howardt12345/keyboard0/PCB/Gerber/Draft 1-1/custom_keyboard (f303, fe2.1) bottom with fill.png

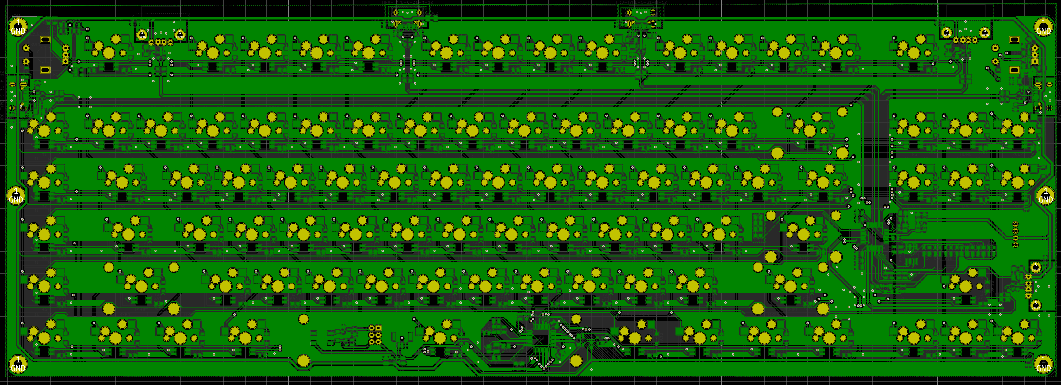
PCB/Gerber/Draft 1-1/custom_keyboard (f303, fe2.1) bottom with fill.png
