howardt12345/keyboard0/PCB/Gerber/Draft 1-2/Images/custom_keyboard (f303, fe2.1) bottom 3d.png

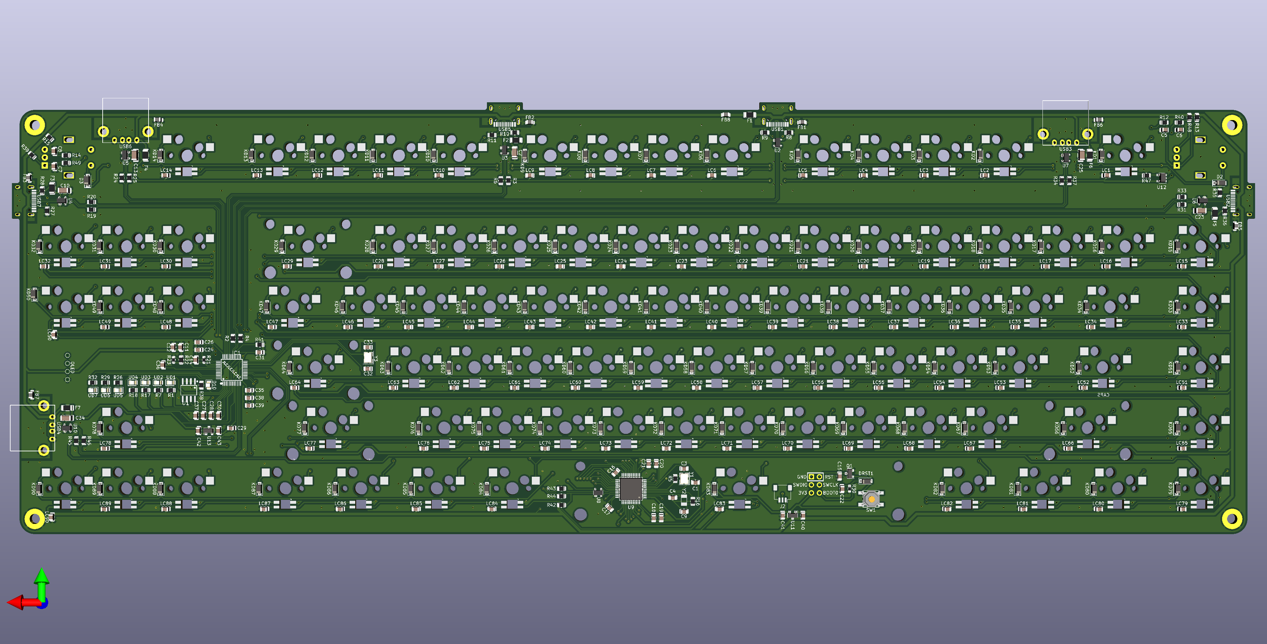
PCB/Gerber/Draft 1-2/Images/custom_keyboard (f303, fe2.1) bottom 3d.png
