howardt12345/keyboard0/PCB/Gerber/Draft 1-2/Images/custom_keyboard (f303, fe2.1) top high contrast.png

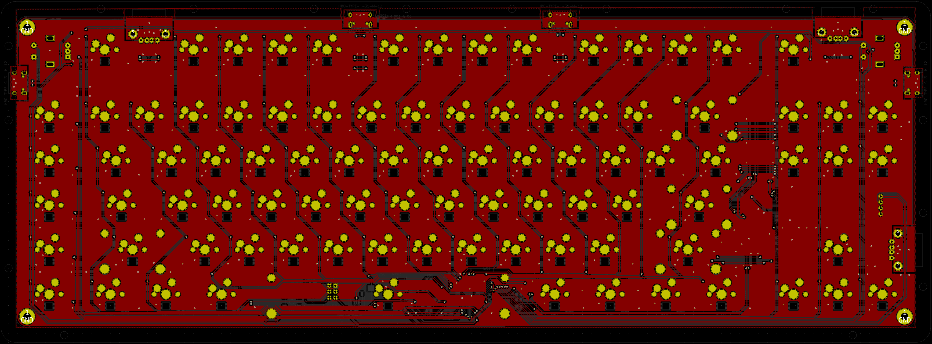
PCB/Gerber/Draft 1-2/Images/custom_keyboard (f303, fe2.1) top high contrast.png
