howardt12345/keyboard0/PCB/Gerber/Draft 1-3/Images/2021-10-26/custom_keyboard (f303, fe2.1) bottom 3d.png

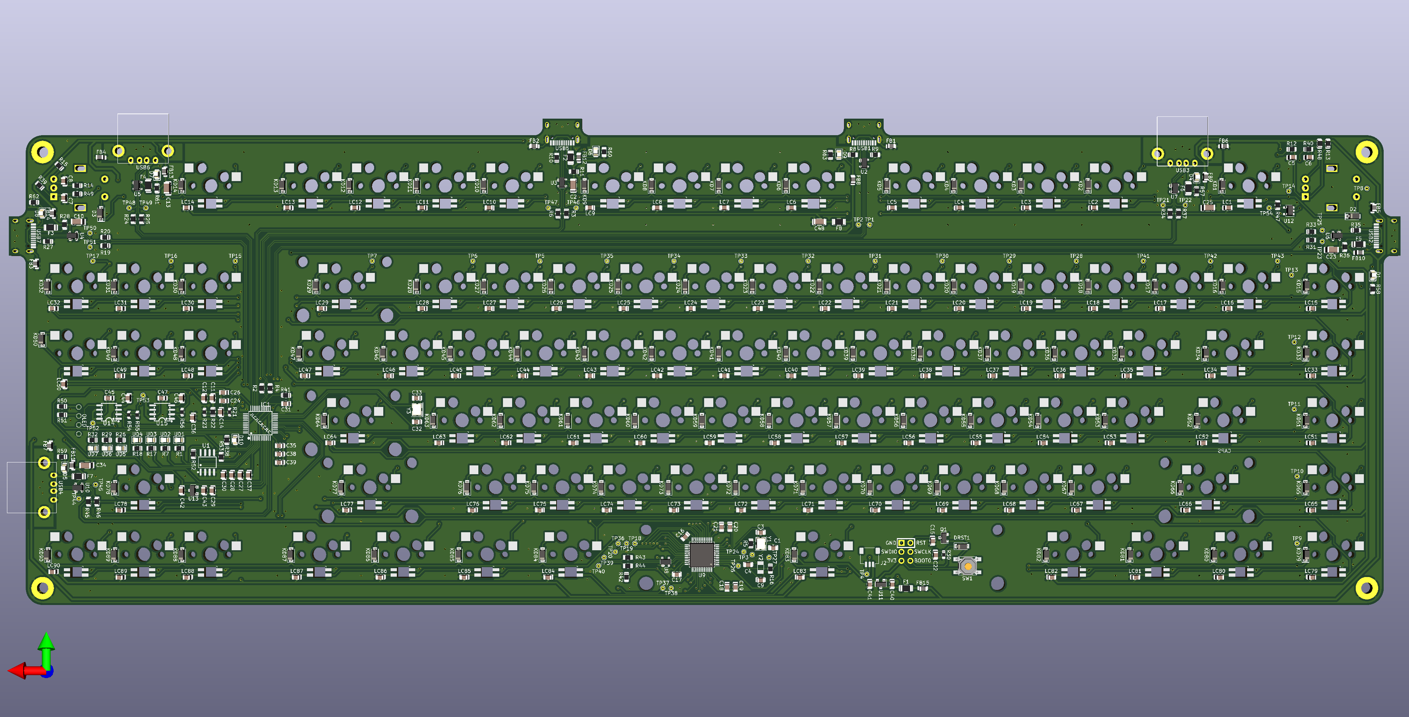
PCB/Gerber/Draft 1-3/Images/2021-10-26/custom_keyboard (f303, fe2.1) bottom 3d.png
