howardt12345/keyboard0/PCB/Gerber/Draft 1-4/Images/2021-10-29/custom_keyboard (f103, fe2.1) bottom fill.png

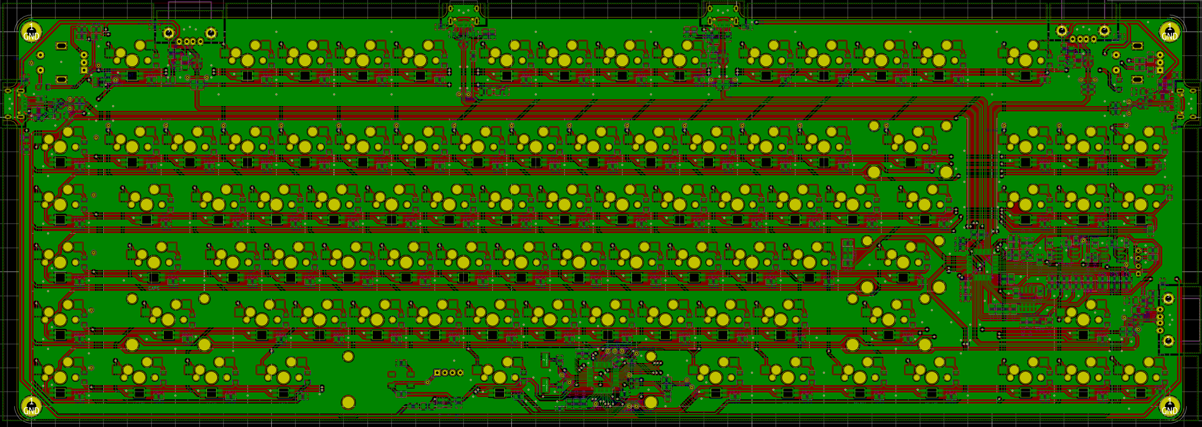
PCB/Gerber/Draft 1-4/Images/2021-10-29/custom_keyboard (f103, fe2.1) bottom fill.png
