howardt12345/keyboard0/PCB/p2/Pics/2.1/keyboard0 bottom.png

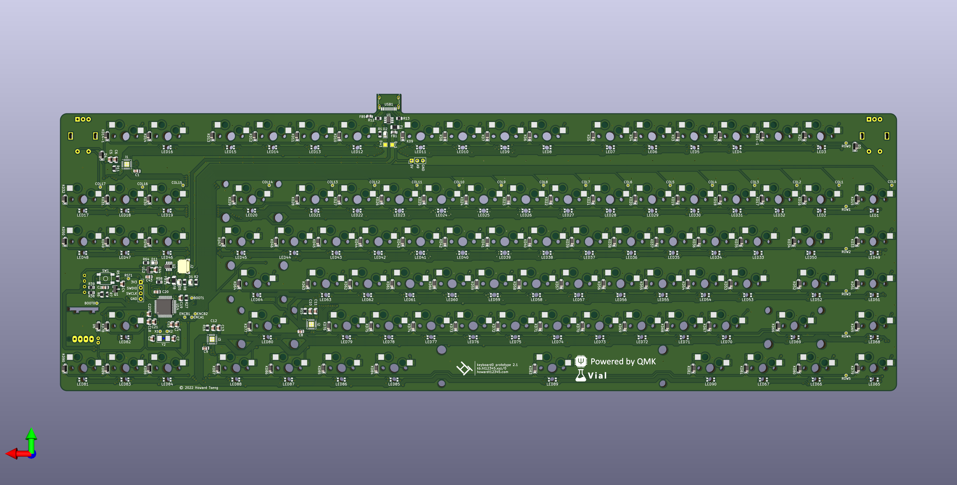
PCB/p2/Pics/2.1/keyboard0 bottom.png
