howardt12345/keyboard0/PCB/p2/Pics/custom_keyboard (f303).png

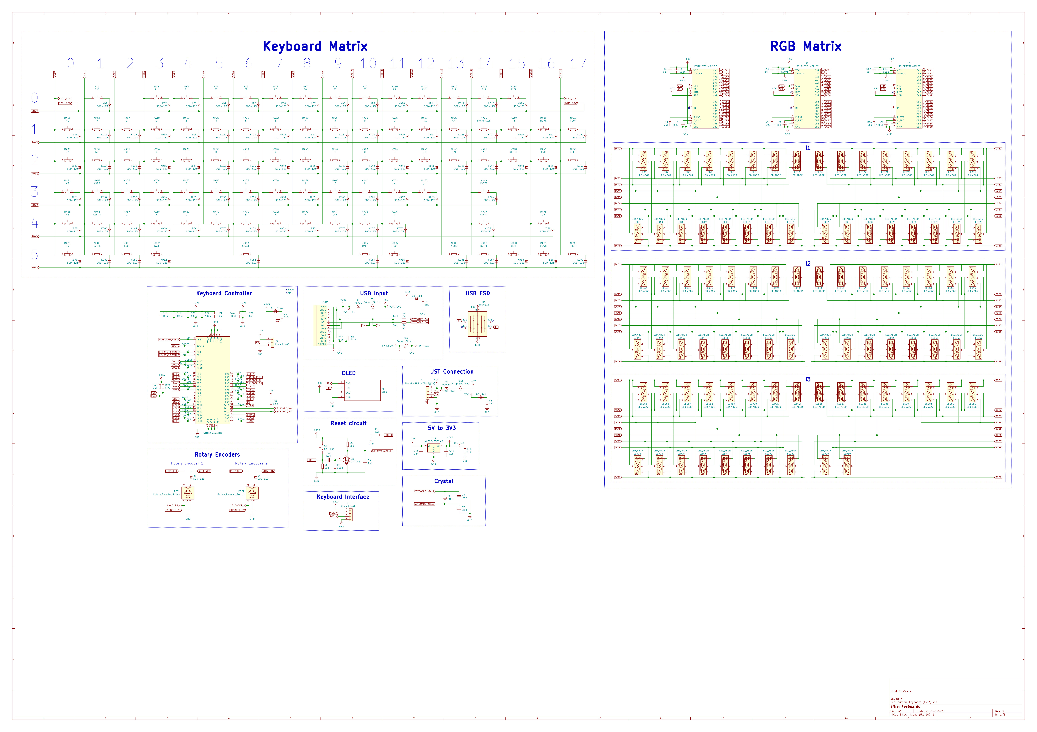
PCB/p2/Pics/custom_keyboard (f303).png
