howardt12345/keyboard0/PCB/p2/Pics/custom_keyboard bottom 3d (1).png

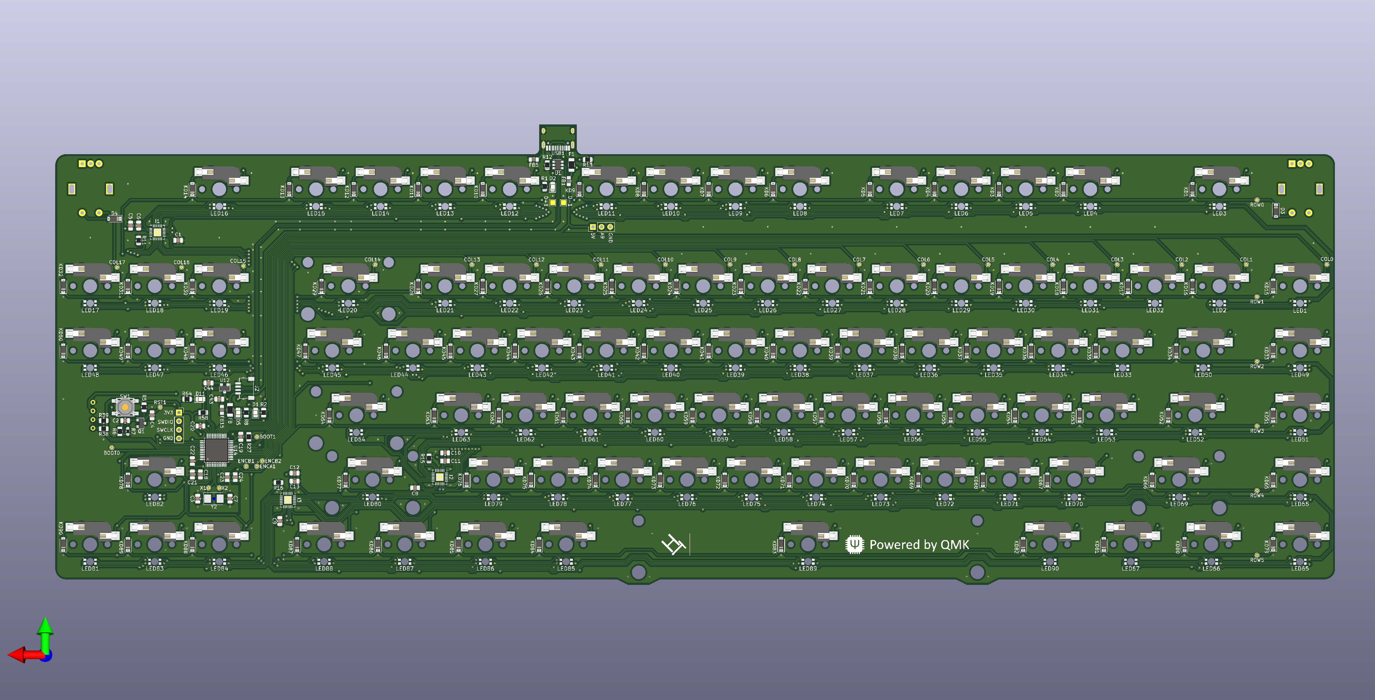
PCB/p2/Pics/custom_keyboard bottom 3d (1).png
