howardt12345/keyboard0/PCB/p2/Pics/custom_keyboard bottom 3d.png

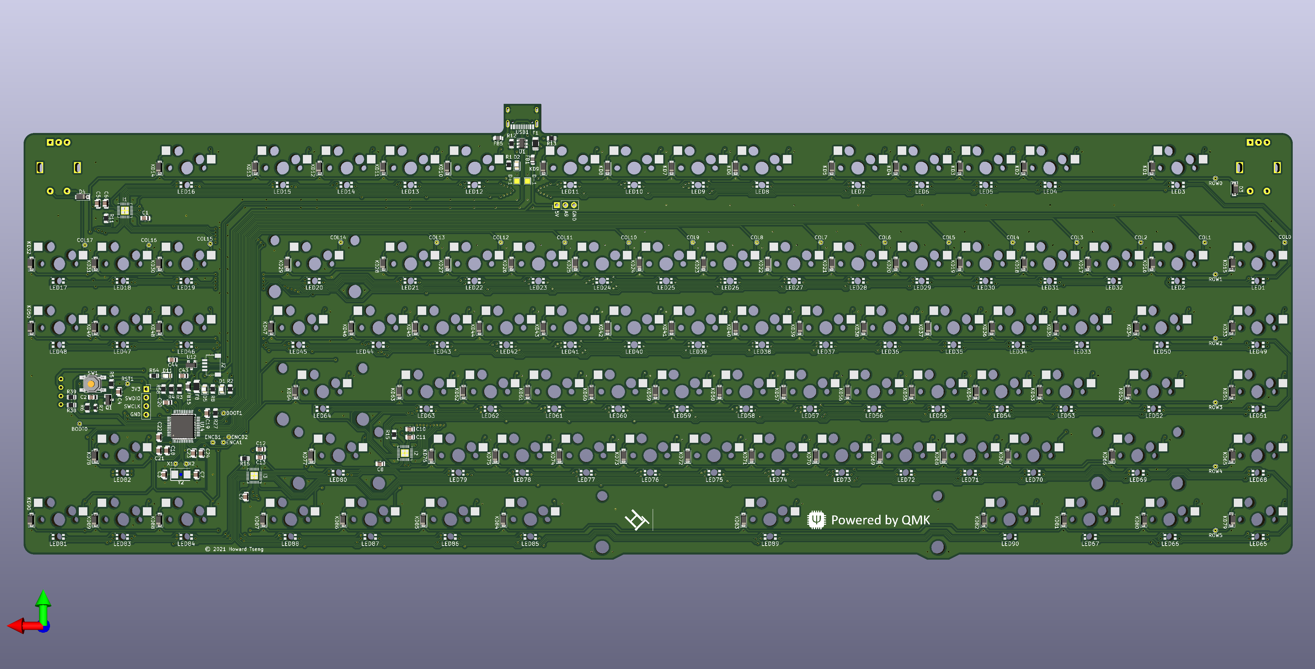
PCB/p2/Pics/custom_keyboard bottom 3d.png
