howardt12345/keyboard0/PCB/p2/Pics/custom_keyboard fill bottom.png

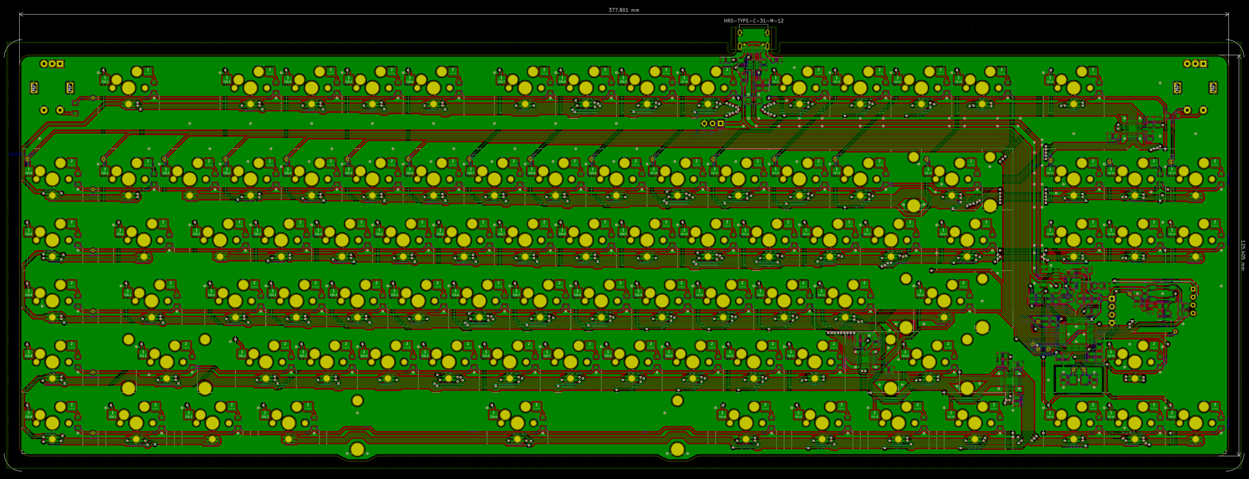
PCB/p2/Pics/custom_keyboard fill bottom.png
