howardt12345/keyboard0/PCB/p2/Pics/custom_keyboard high contrast bottom.png

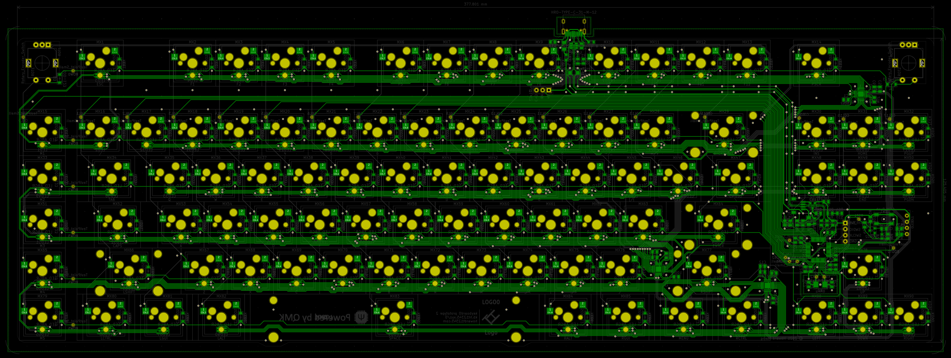
PCB/p2/Pics/custom_keyboard high contrast bottom.png
