howardt12345/keyboard0/PCB/p2/Pics/custom_keyboard MCU area.png

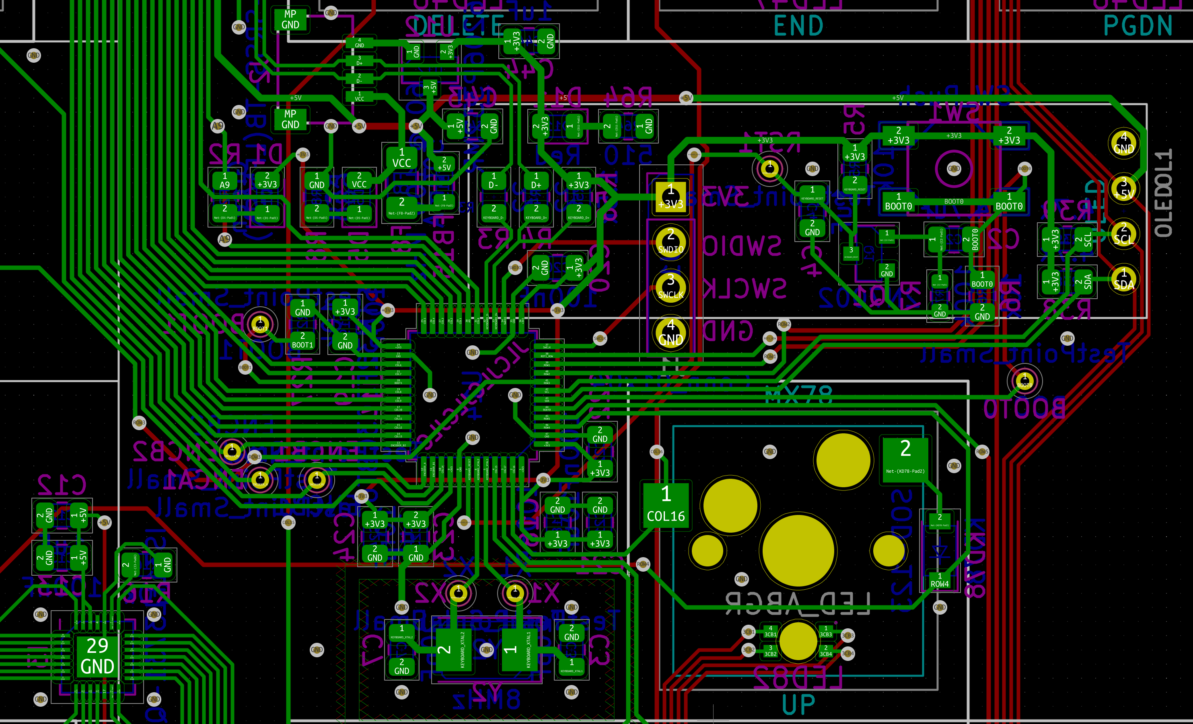
PCB/p2/Pics/custom_keyboard MCU area.png
