howardt12345/keyboard0/PCB/p2/Pics/custom_keyboard traces.png

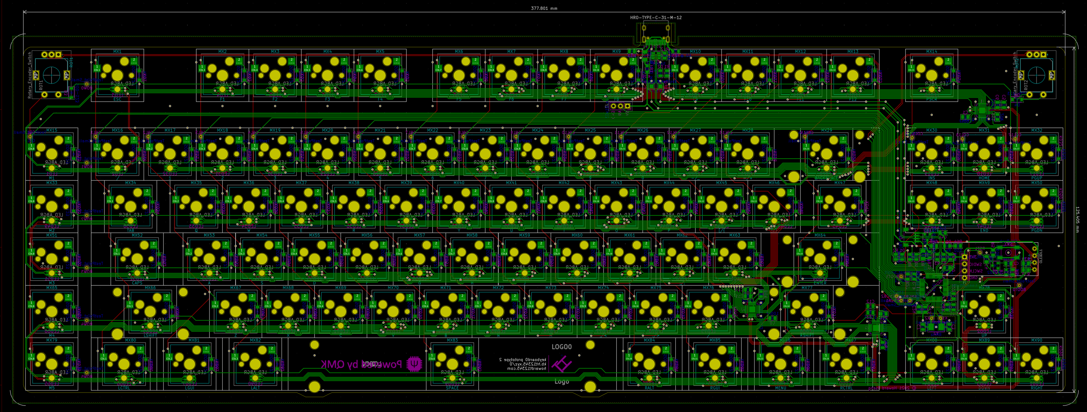
PCB/p2/Pics/custom_keyboard traces.png
