howardt12345/keyboard0/PCB/p2/Pics/custom_keyboard USB area.png

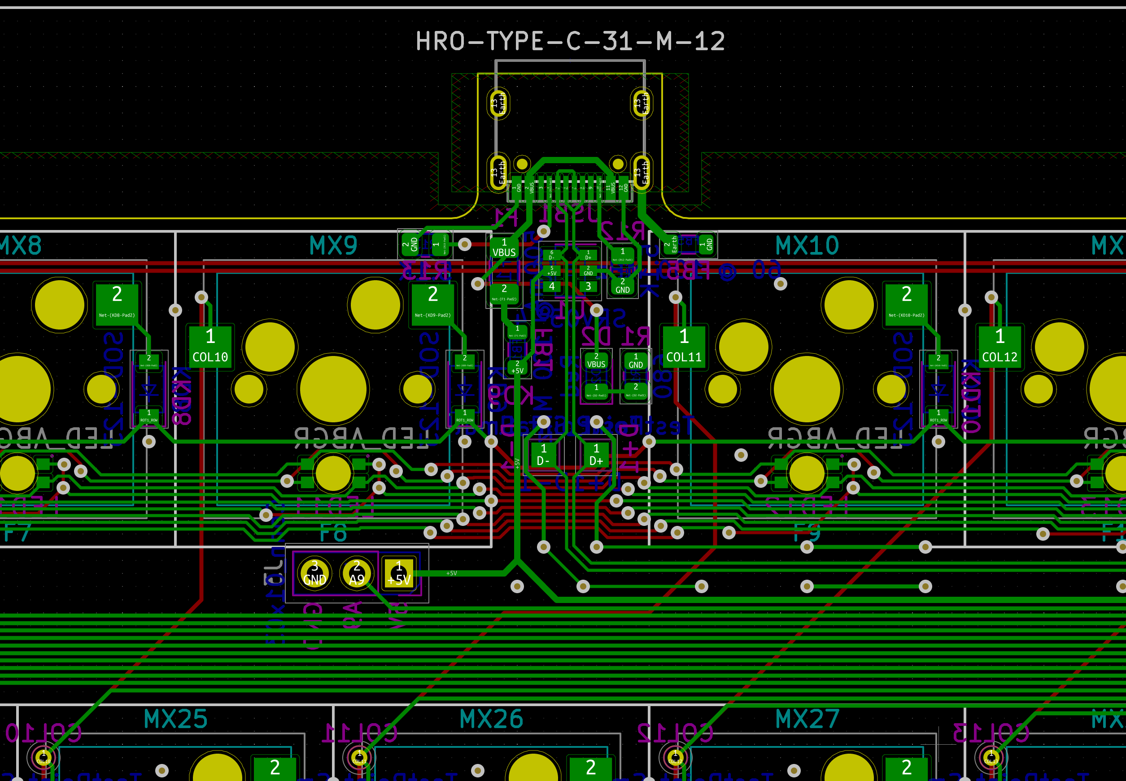
PCB/p2/Pics/custom_keyboard USB area.png
