howardt12345/keyboard0/PCB/p3/Pics/keyboard0-top.png

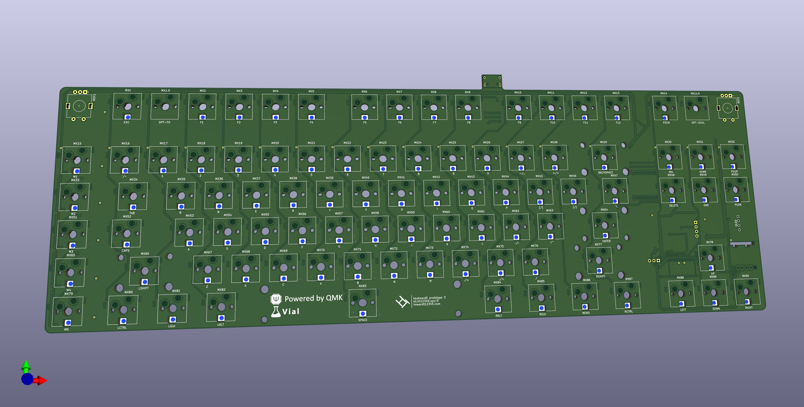
PCB/p3/Pics/keyboard0-top.png
