howardt12345/keyboard0/PCB/Plate/v3/Assets/custom_keyboard plate v3 bottom tpe 3.png

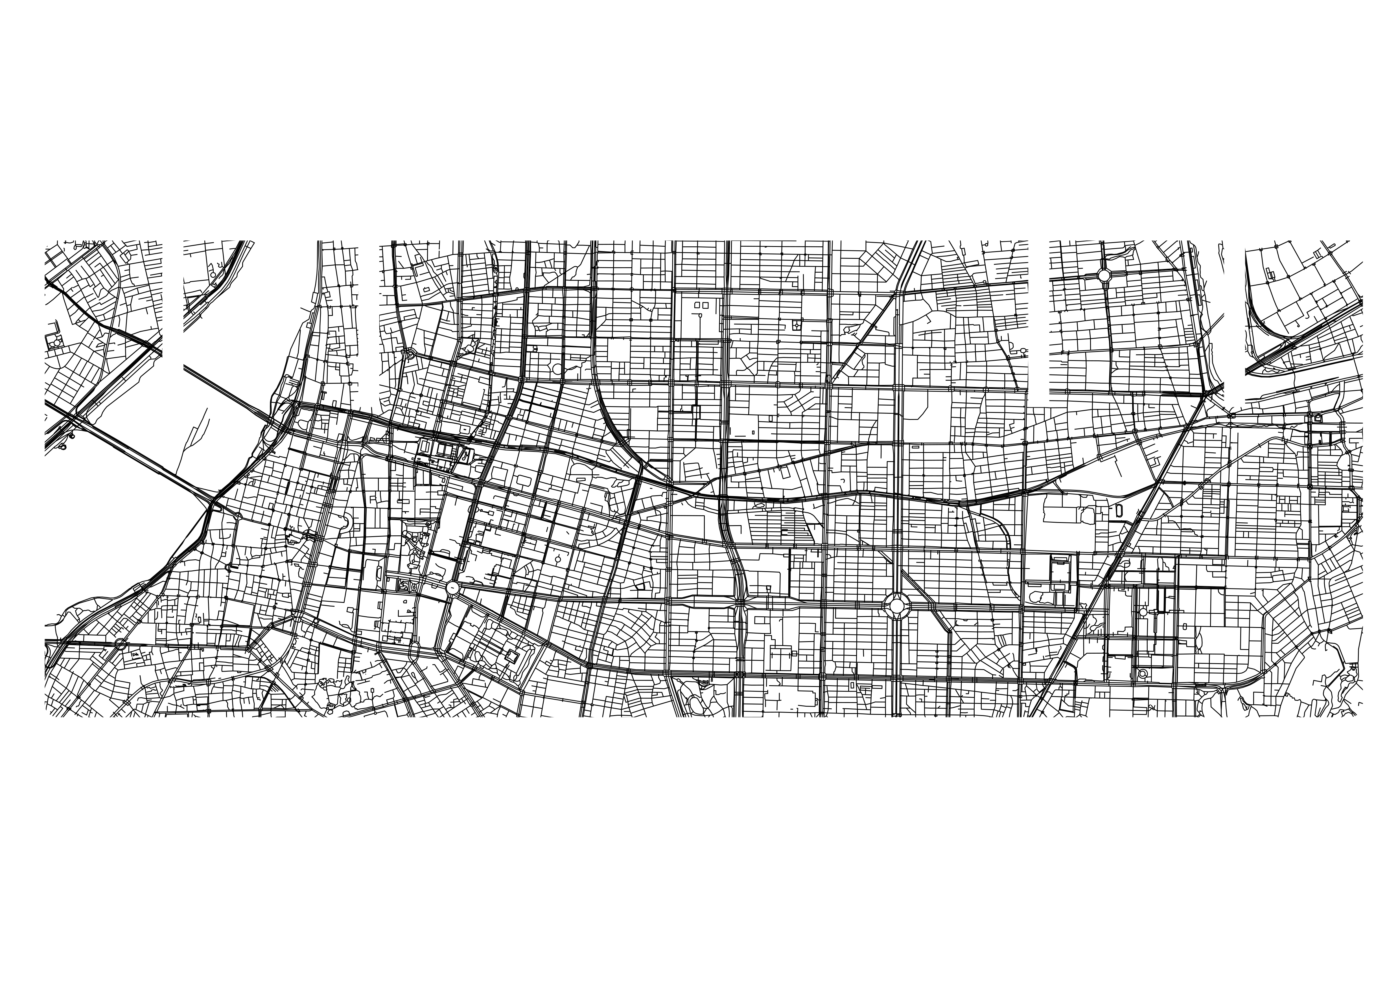
PCB/Plate/v3/Assets/custom_keyboard plate v3 bottom tpe 3.png
