howardt12345/keyboard0/PCB/Plate/v3/Assets/custom_keyboard plate v3 to.png

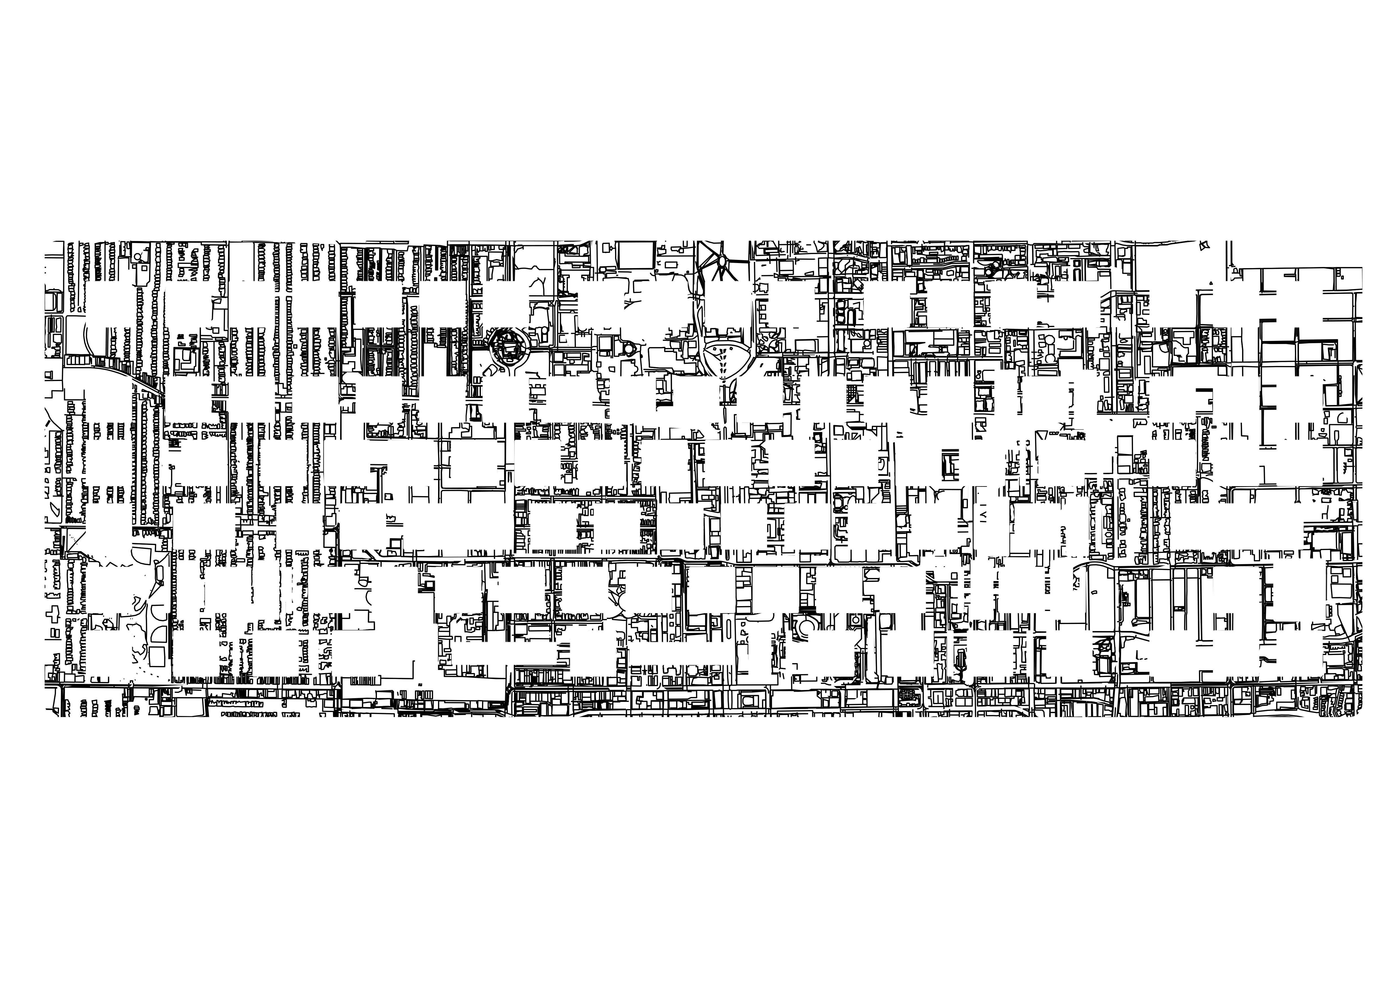
PCB/Plate/v3/Assets/custom_keyboard plate v3 to.png
