howardt12345/keyboard0/Case/v3 middle parts/3d print/Layer 4 1.stl

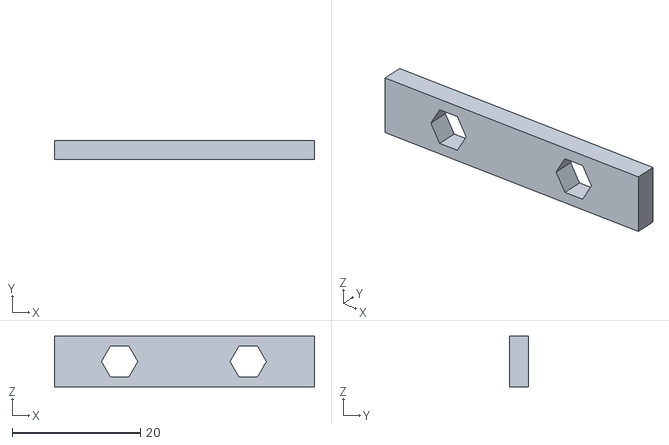
[picture p82: CAD file, 2022-03-12]
Case/v3 middle parts/3d print/Layer 4 1.stl
40.5 x 3.00 x 7.94
