howardt12345/keyboard0/Case/v3 middle parts/3d print/Layer 4 3.stl

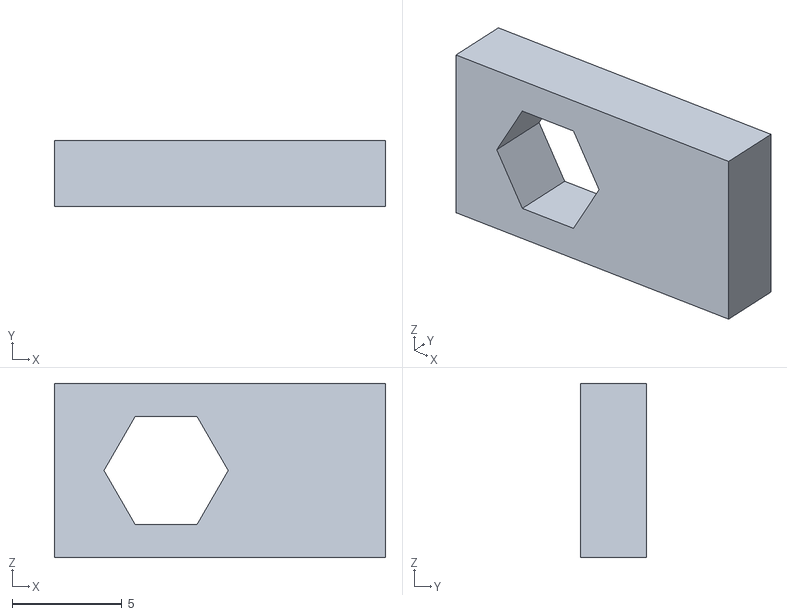
[picture p83: CAD file, 2022-03-12]
Case/v3 middle parts/3d print/Layer 4 3.stl
15.1 x 3.00 x 7.94
