howardt12345/keyboard0/Case/v3 middle parts/3d print/Layer 1-3 7.stl

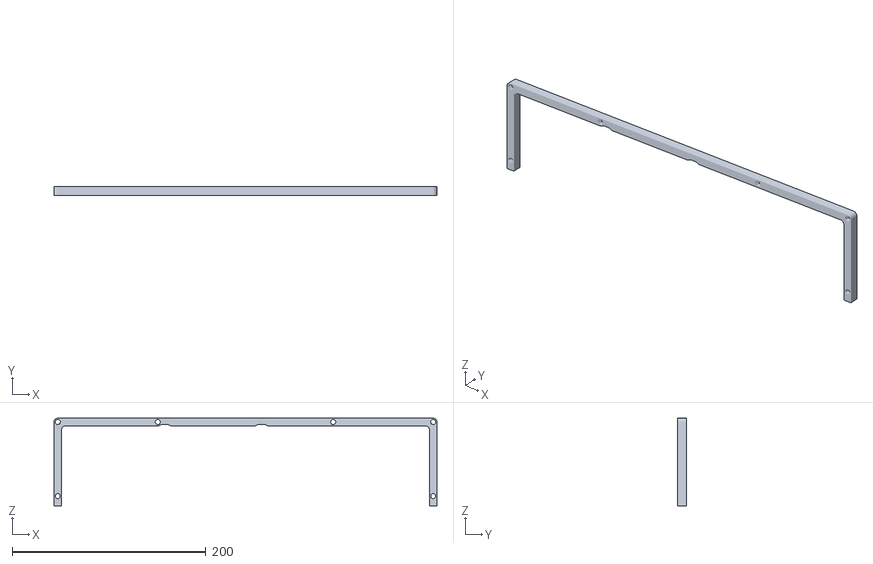
[picture p84: CAD file, 2022-03-12]
Case/v3 middle parts/3d print/Layer 1-3 7.stl
395.3 x 9.00 x 90.5
